CreatorKanata/3d-printed-running-shoes/images/3d-cad/asm-honeycomb-front.png

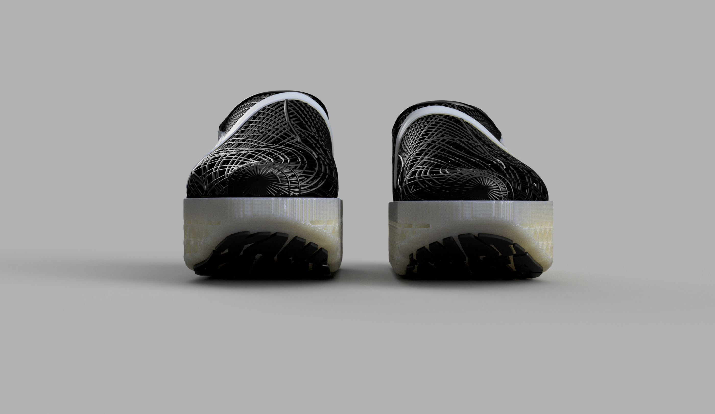
images/3d-cad/asm-honeycomb-front.png
