CreatorKanata/3d-printed-running-shoes/images/report/adidas-store.png

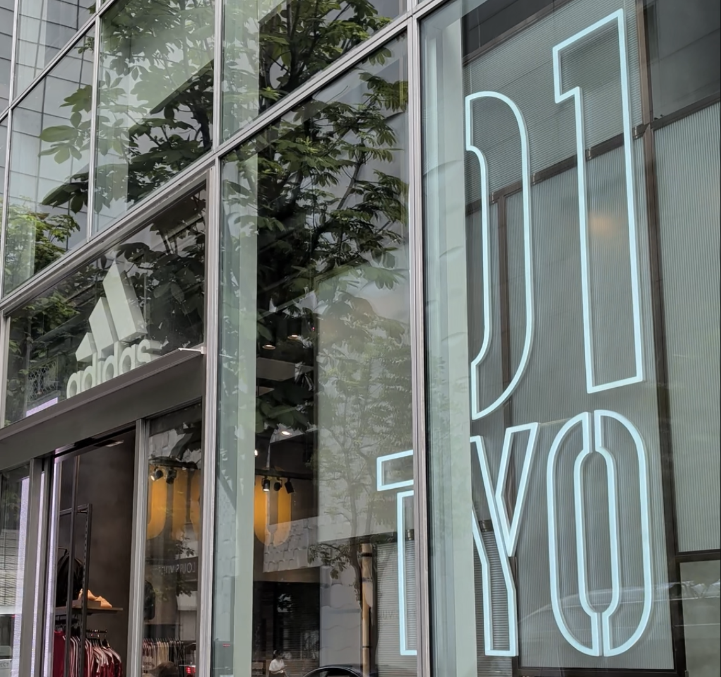
images/report/adidas-store.png
