CreatorKanata/3d-printed-running-shoes/images/report/competitive-analysis.jpg

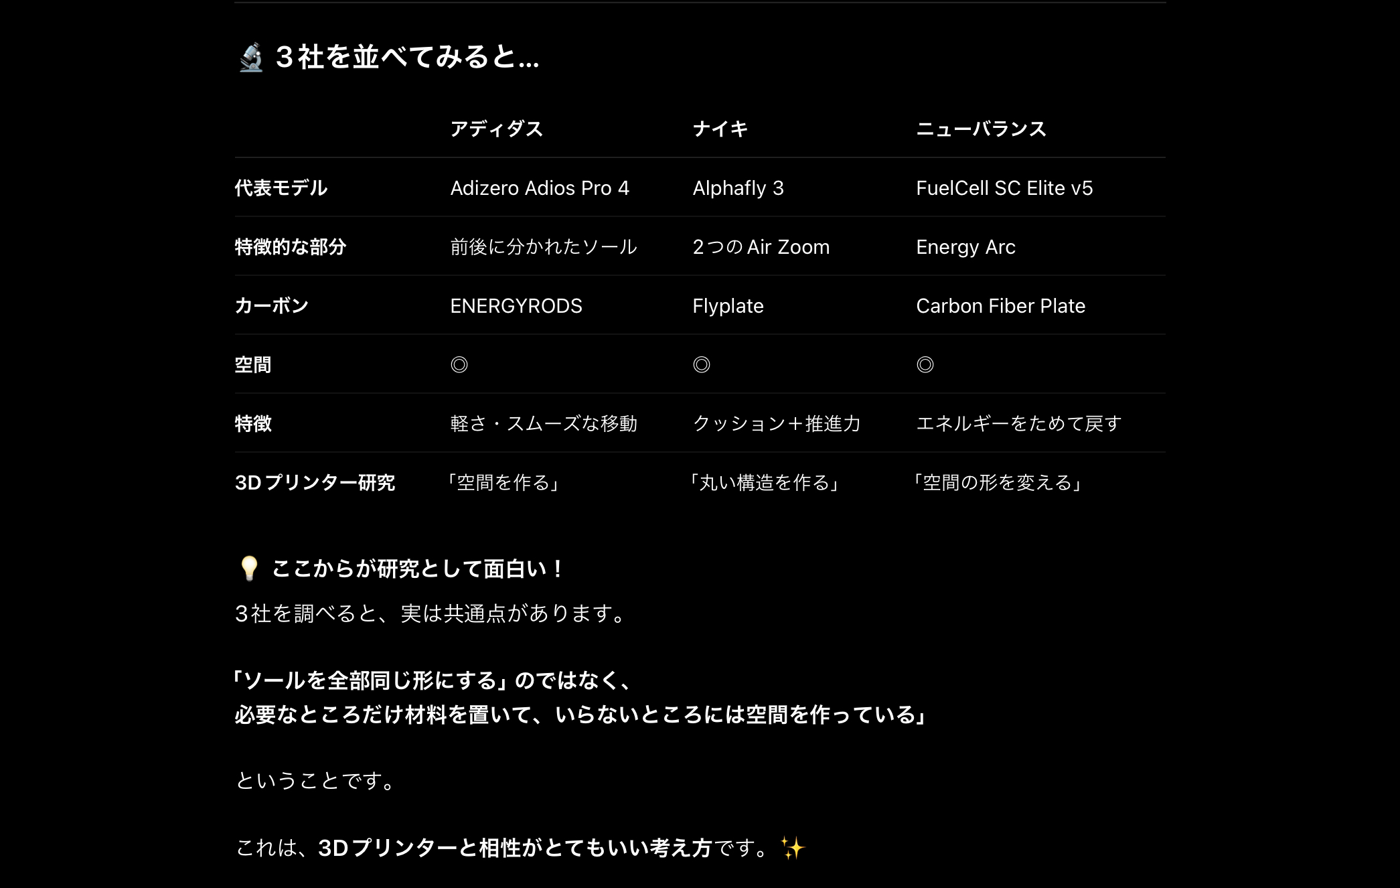
images/report/competitive-analysis.jpg
