CreatorKanata/3d-printed-running-shoes/images/report/competitor-adidas.png

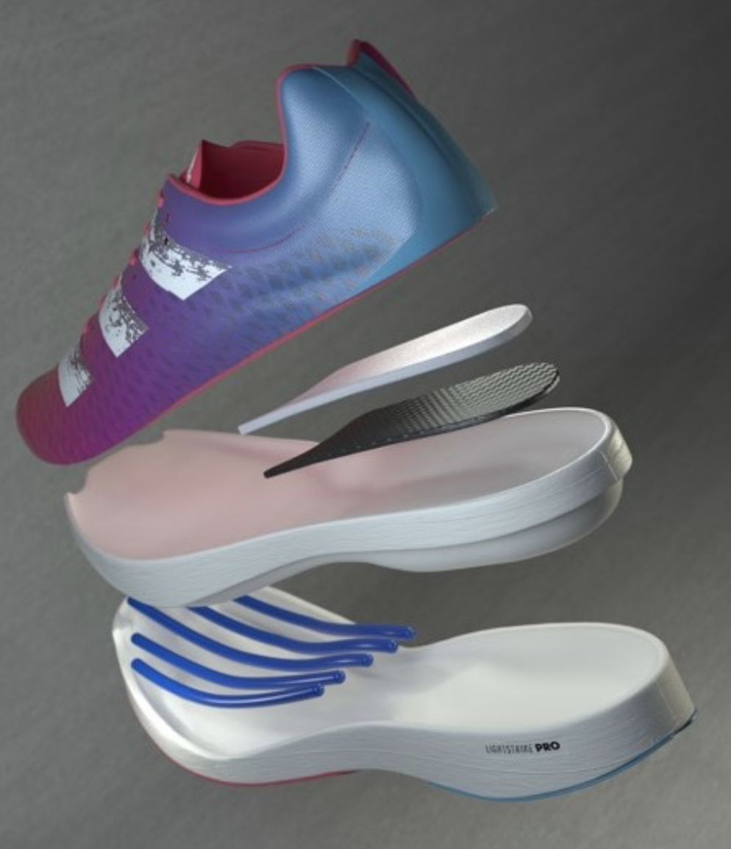
images/report/competitor-adidas.png
