CreatorKanata/3d-printed-running-shoes/images/report/competitor-new-balance.png

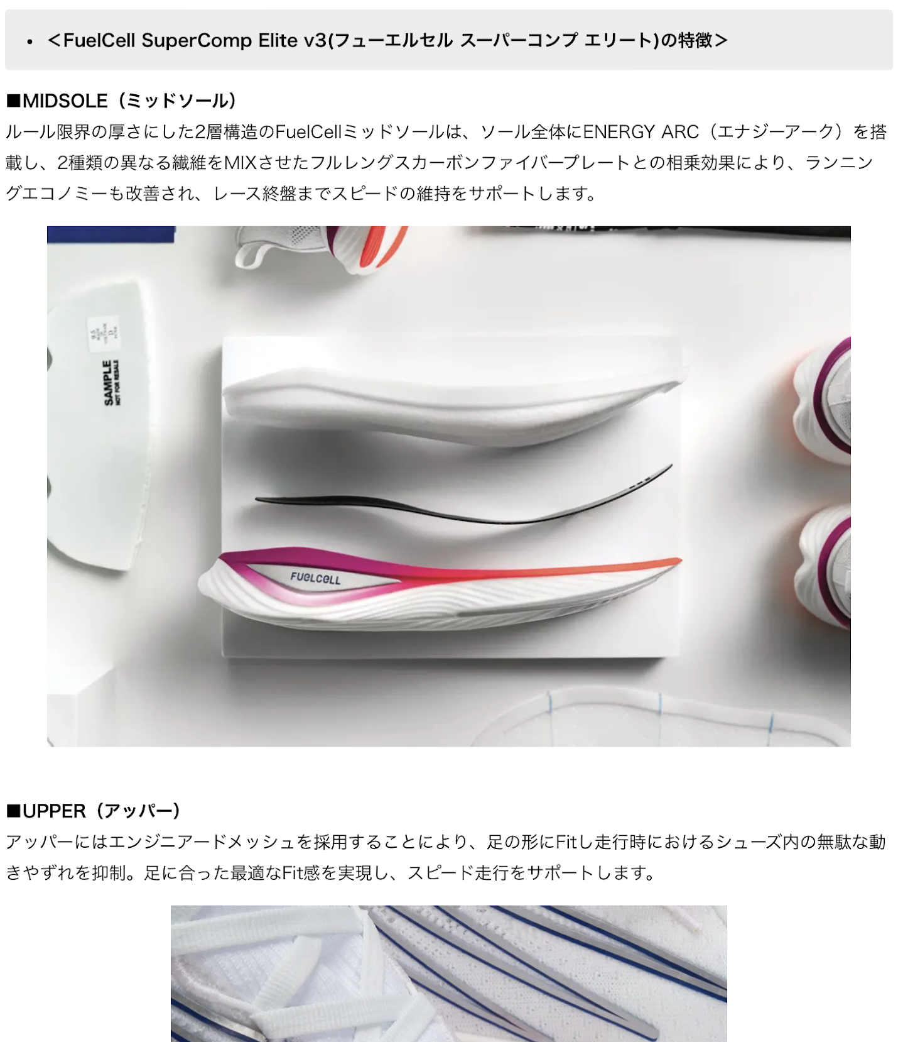
images/report/competitor-new-balance.png
