CreatorKanata/3d-printed-running-shoes/images/report/glue-shoes.png

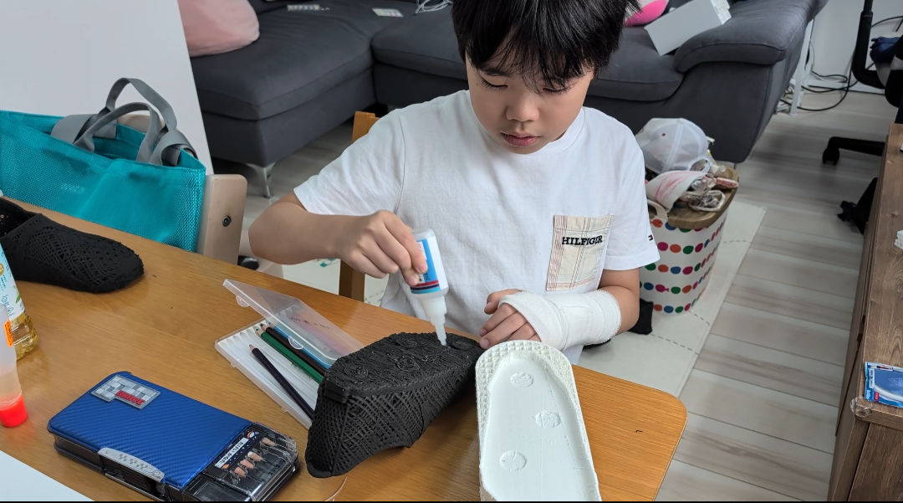
images/report/glue-shoes.png
