CreatorKanata/3d-printed-running-shoes/images/report/insert-insole.png

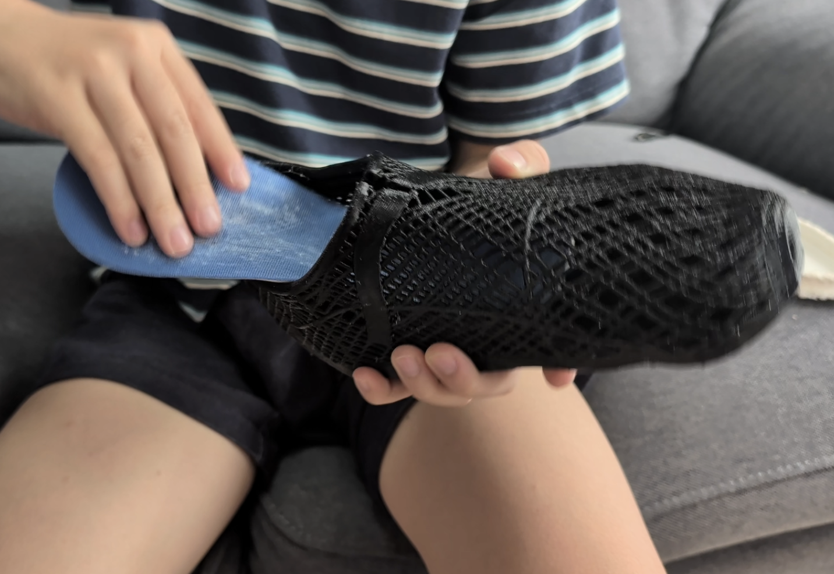
images/report/insert-insole.png
