CreatorKanata/3d-printed-running-shoes/images/report/pc-plate1.jpg

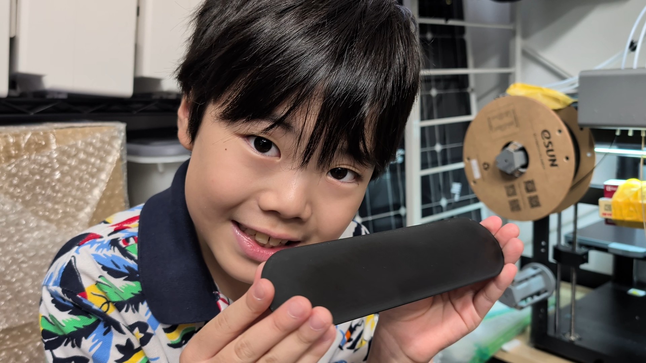
images/report/pc-plate1.jpg
