CreatorKanata/3d-printed-running-shoes/images/report/pc-plate-placement2.png

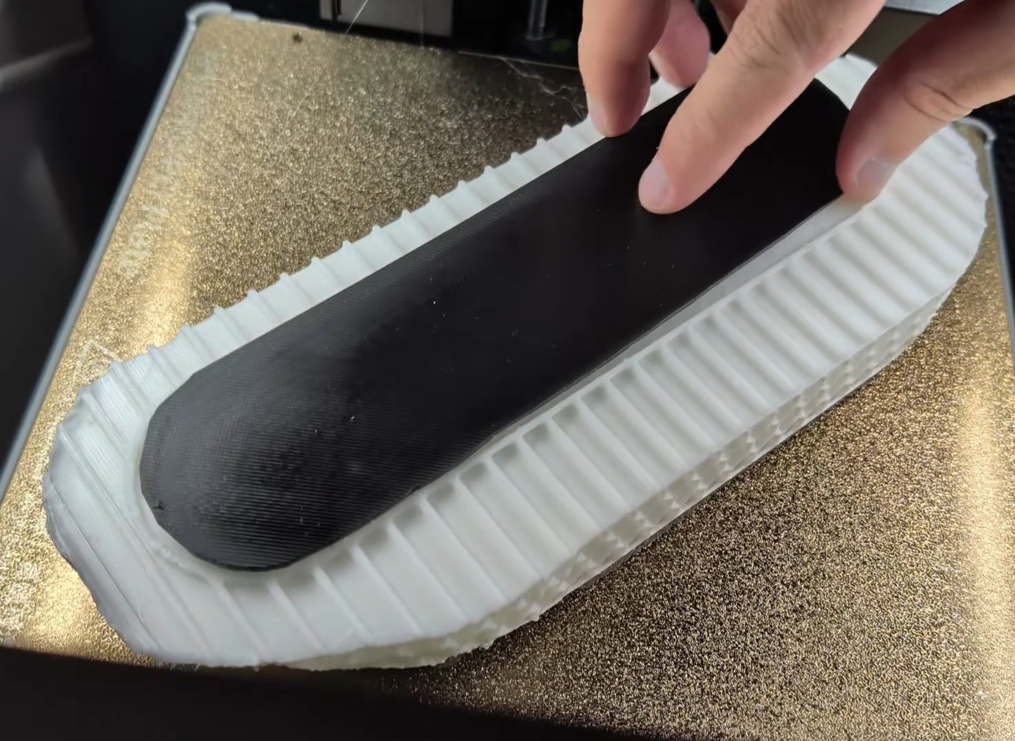
images/report/pc-plate-placement2.png
