CreatorKanata/3d-printed-running-shoes/images/report/running-side-view1.png

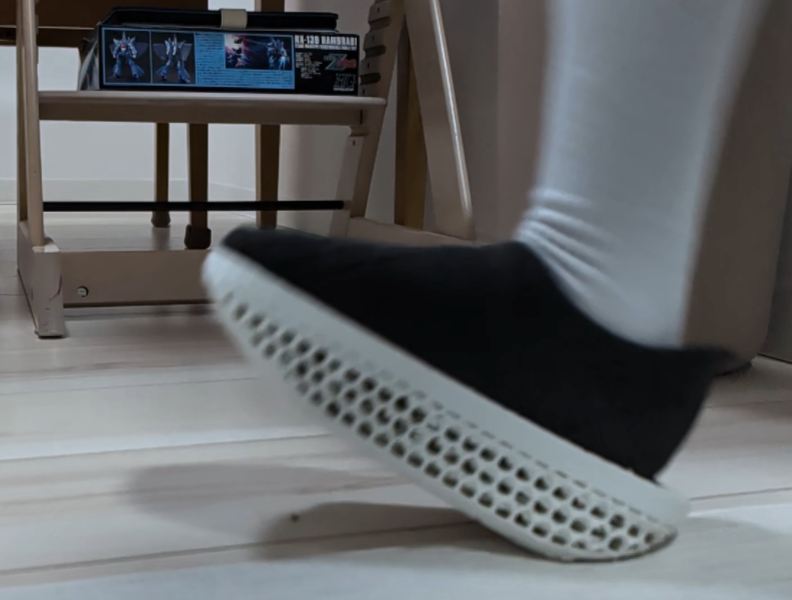
images/report/running-side-view1.png
