CreatorKanata/3d-printed-running-shoes/images/report/weight-normal.jpg

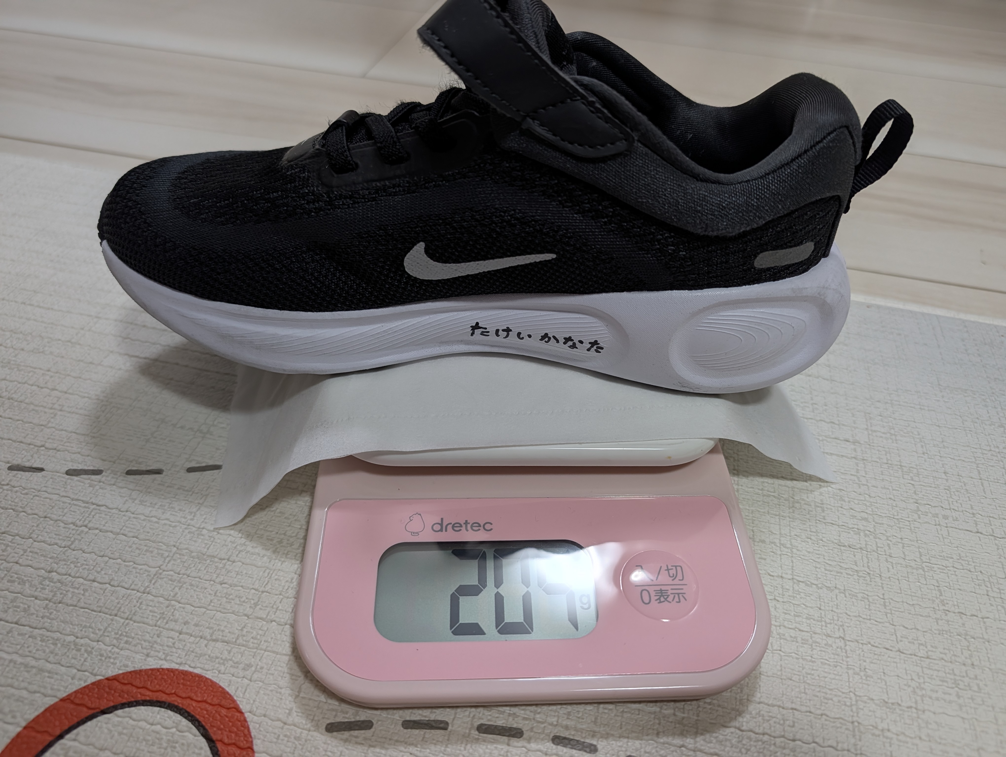
images/report/weight-normal.jpg
