CreatorKanata/3d-printed-running-shoes/images/report/weight-v1.jpg

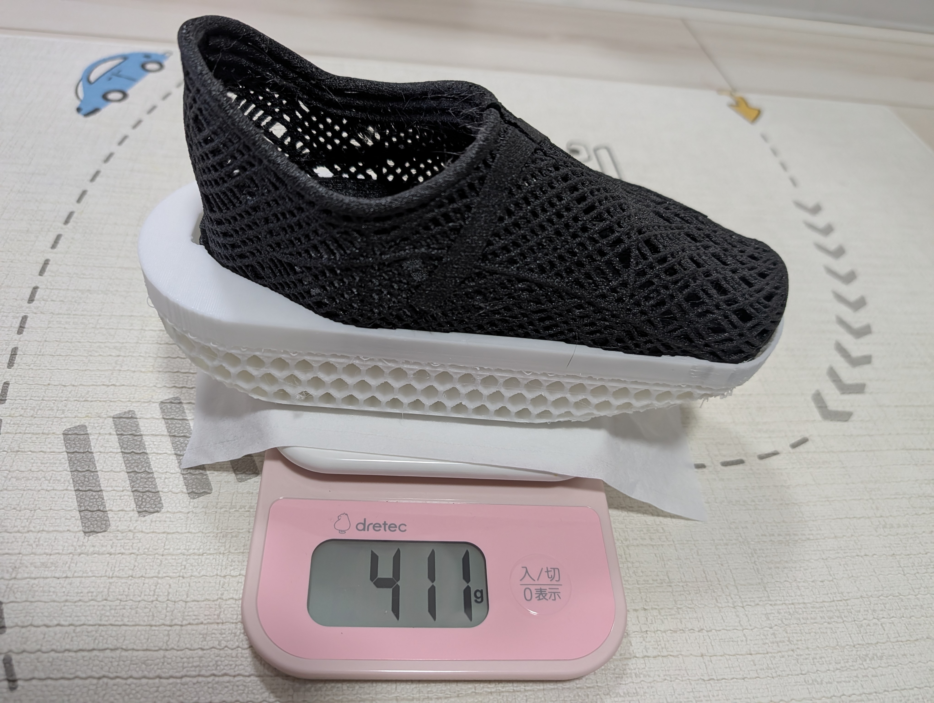
images/report/weight-v1.jpg
