CreatorKanata/3d-printed-running-shoes/images/report/weight-v2.jpg

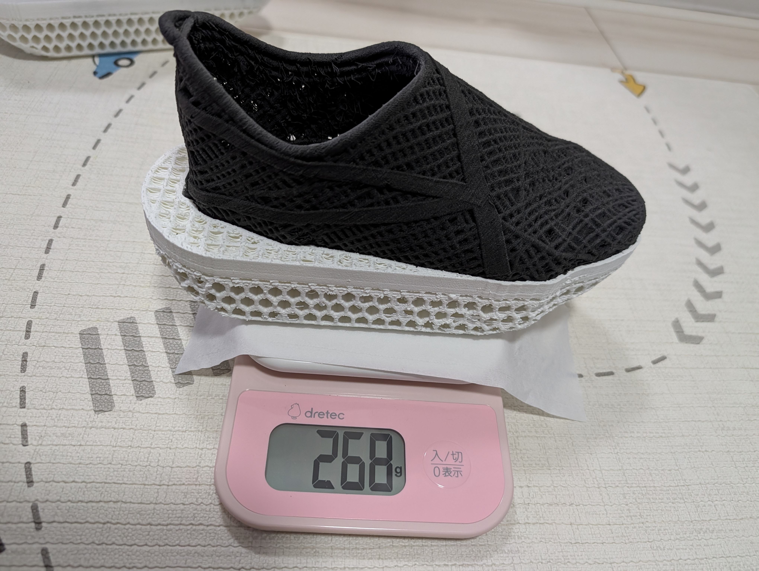
images/report/weight-v2.jpg
