CreatorKanata/3d-printed-running-shoes/images/report/3d-print-slicer.jpg

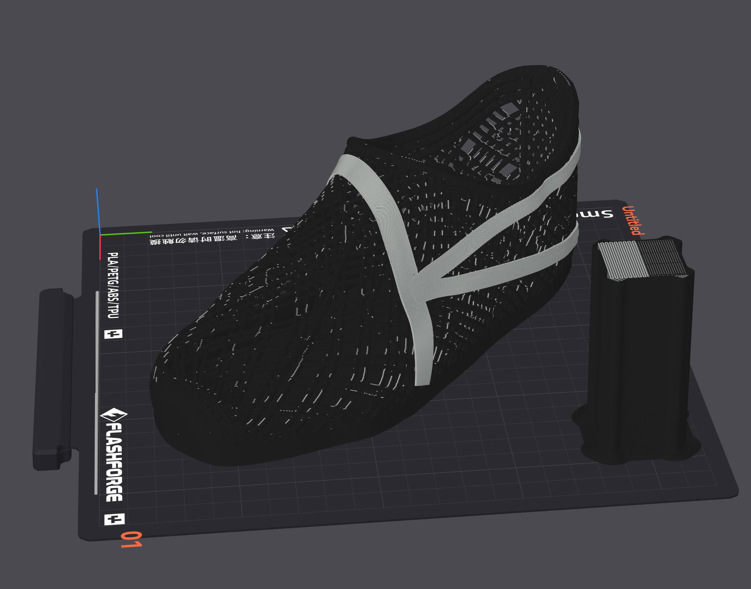
images/report/3d-print-slicer.jpg
