CreatorKanata/3d-printed-running-shoes/images/report/first-shoe-upper-printing.jpg

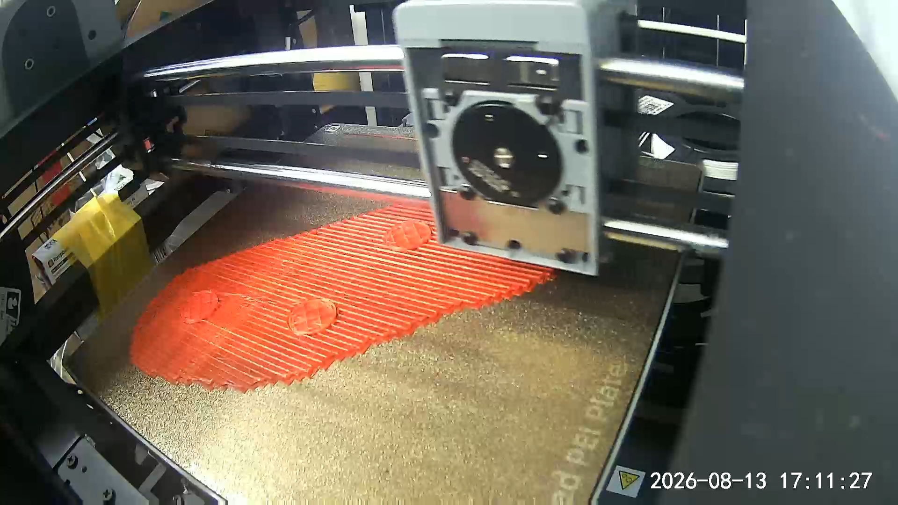
images/report/first-shoe-upper-printing.jpg
