CreatorKanata/3d-printed-running-shoes/images/report/shoe-upper-printing.png

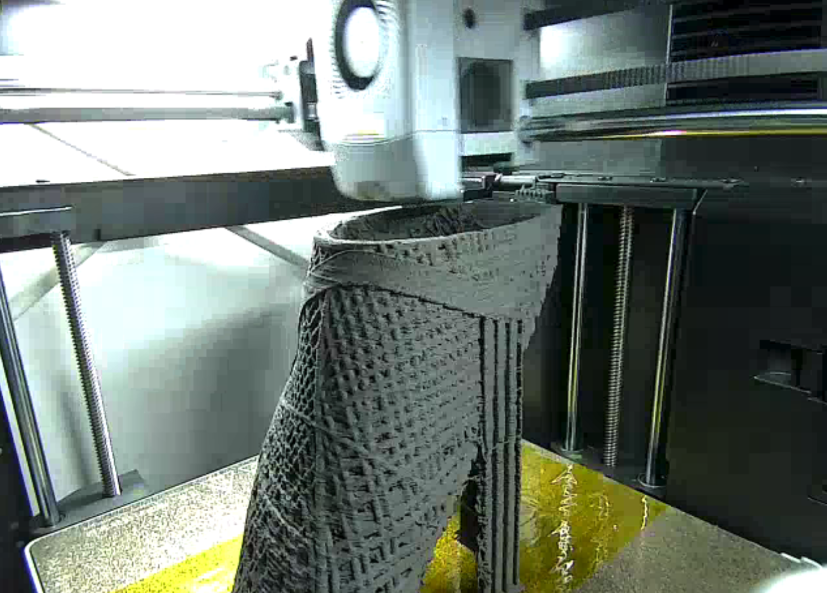
images/report/shoe-upper-printing.png
