CreatorKanata/3d-printed-running-shoes/images/report/running-test0.png

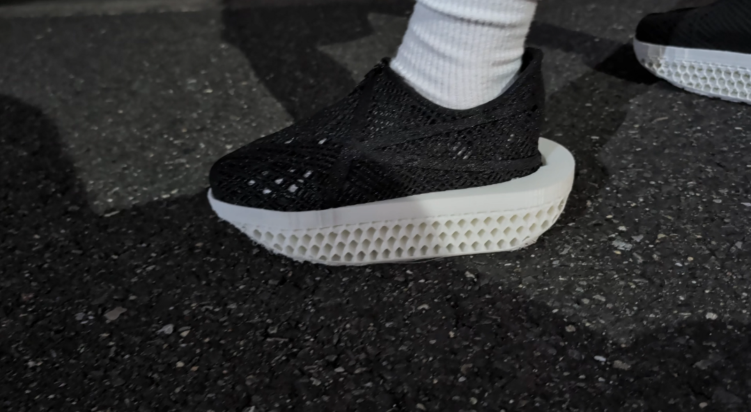
images/report/running-test0.png
