CreatorKanata/3d-printed-running-shoes/images/report/running-test2.png

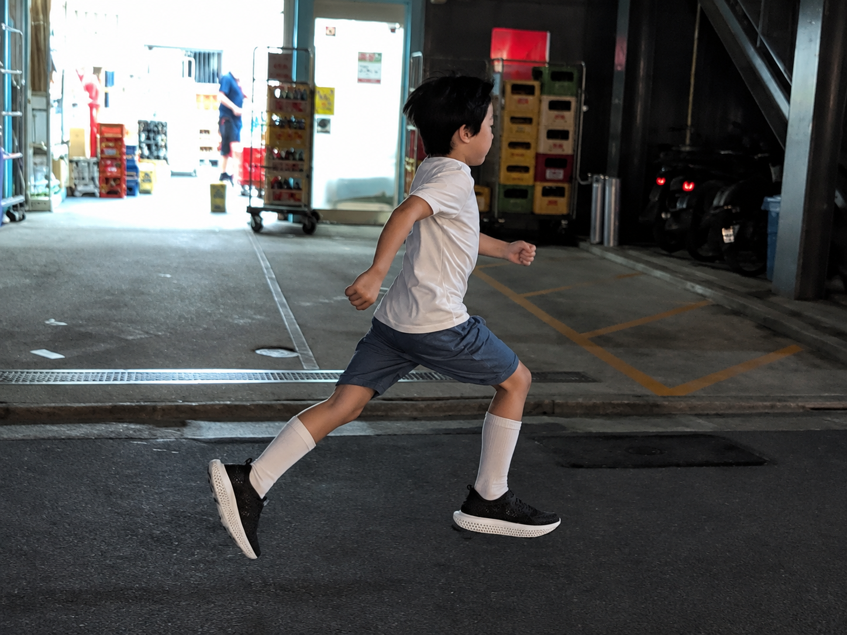
images/report/running-test2.png
