CreatorKanata/3d-printed-running-shoes/images/report/running-test-normal.png

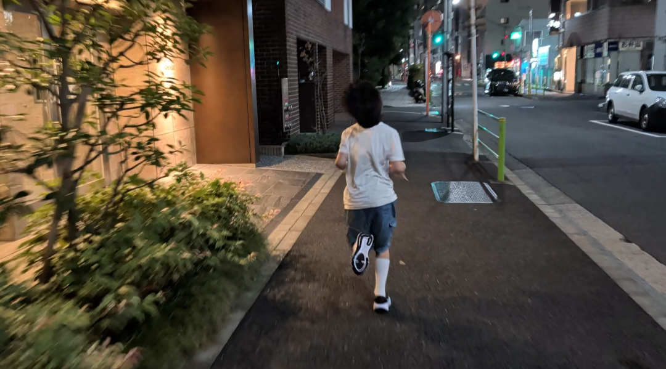
images/report/running-test-normal.png
